tomhogue/Digital_Carb_Sync_Shield/CarbSync_CD_2015July/Pictures/before heating.JPG

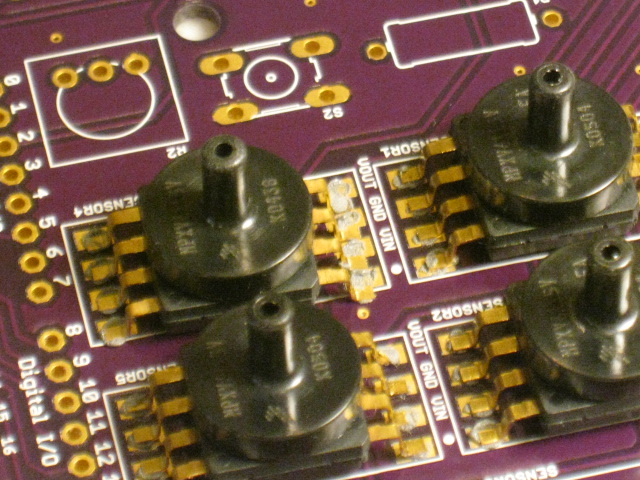
CarbSync_CD_2015July/Pictures/before heating.JPG
