tomhogue/Digital_Carb_Sync_Shield/CarbSync_CD_2015July/Pictures/complete x4.jpg

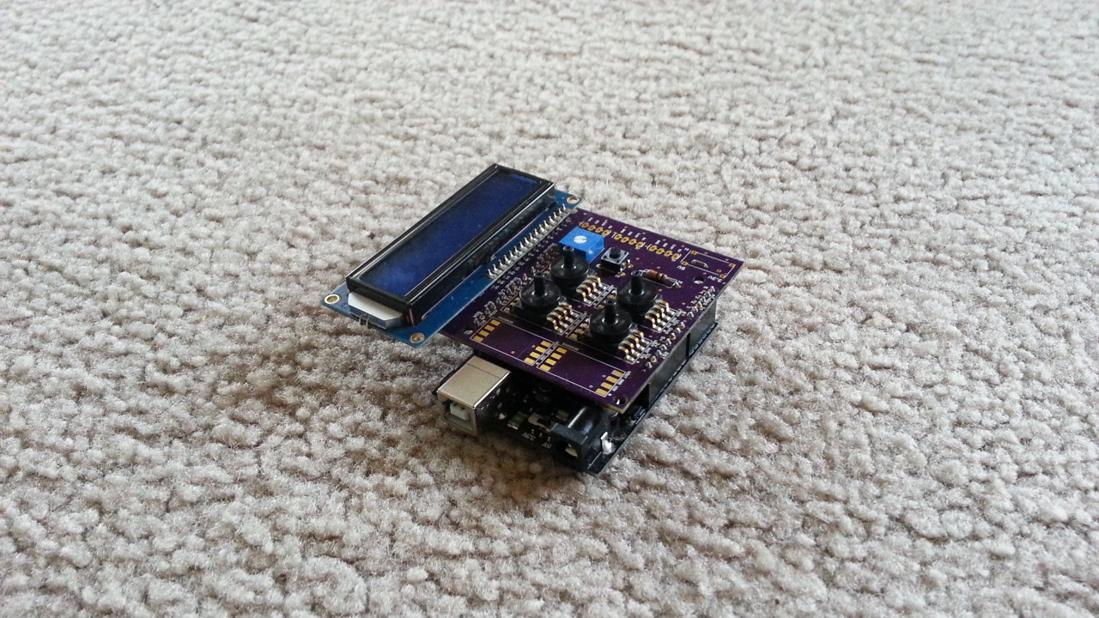
CarbSync_CD_2015July/Pictures/complete x4.jpg
