tomhogue/Digital_Carb_Sync_Shield/CarbSync_CD_2015July/Pictures/cooling.JPG

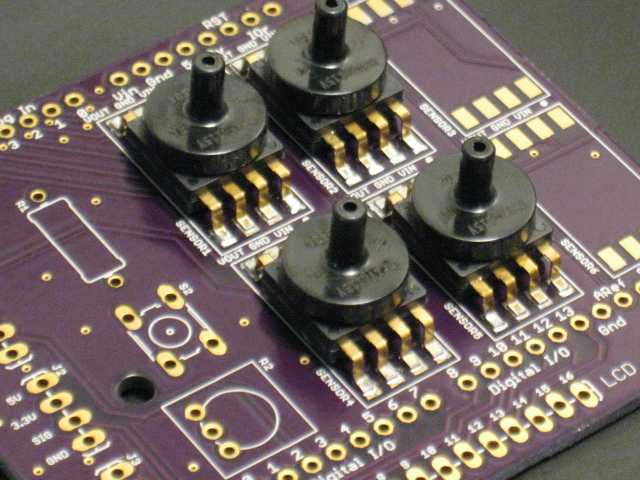
CarbSync_CD_2015July/Pictures/cooling.JPG
