tomhogue/Digital_Carb_Sync_Shield/CarbSync_CD_2015July/Pictures/headers to attach to UNO.JPG

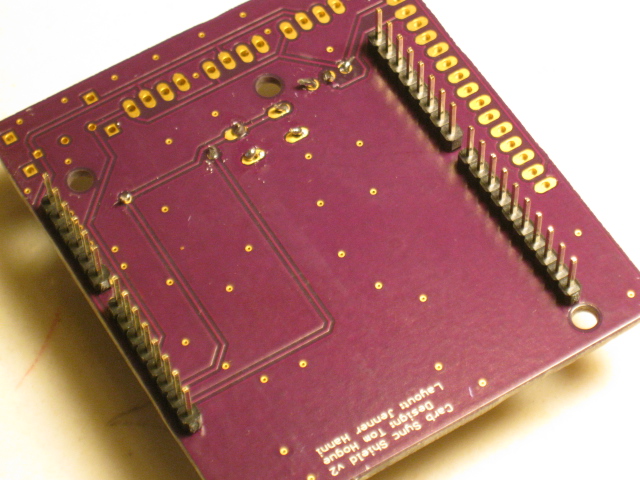
CarbSync_CD_2015July/Pictures/headers to attach to UNO.JPG
