tomhogue/Digital_Carb_Sync_Shield/CarbSync_CD_2015July/Pictures/IMG_0836.JPG

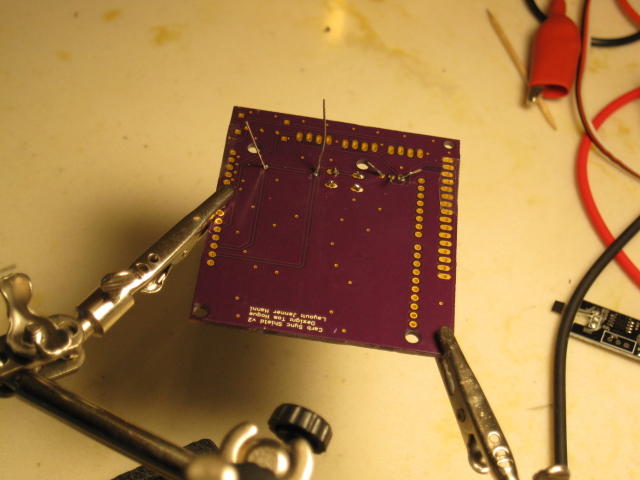
CarbSync_CD_2015July/Pictures/IMG_0836.JPG
