tomhogue/Digital_Carb_Sync_Shield/CarbSync_CD_2015July/Pictures/in use 02.JPG

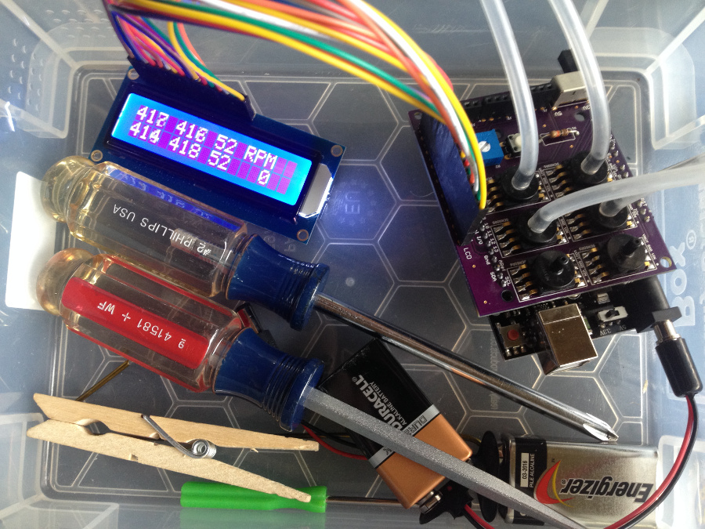
CarbSync_CD_2015July/Pictures/in use 02.JPG
