tomhogue/Digital_Carb_Sync_Shield/CarbSync_CD_2015July/Pictures/joints.gif

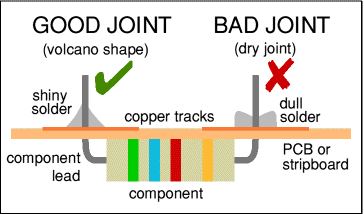
CarbSync_CD_2015July/Pictures/joints.gif
