tomhogue/Digital_Carb_Sync_Shield/CarbSync_CD_2015July/Pictures/Notch and dot.JPG

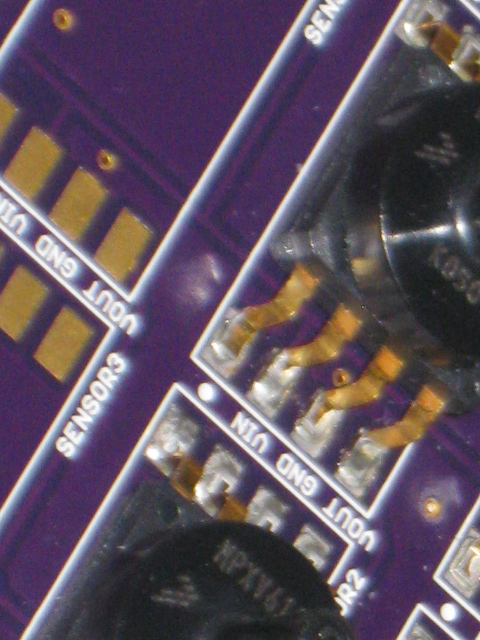
CarbSync_CD_2015July/Pictures/Notch and dot.JPG
