tomhogue/Digital_Carb_Sync_Shield/CarbSync_CD_2015July/Pictures/powered up 2015.jpg

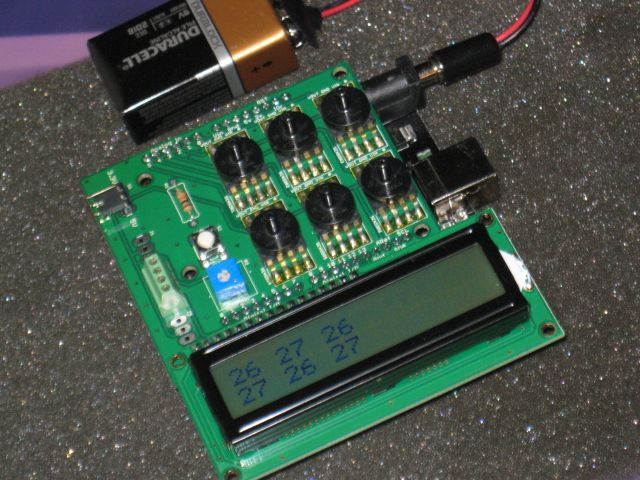
CarbSync_CD_2015July/Pictures/powered up 2015.jpg
