tomhogue/Digital_Carb_Sync_Shield/CarbSync_CD_2015July/Pictures/Header_Joints_guide.jpg

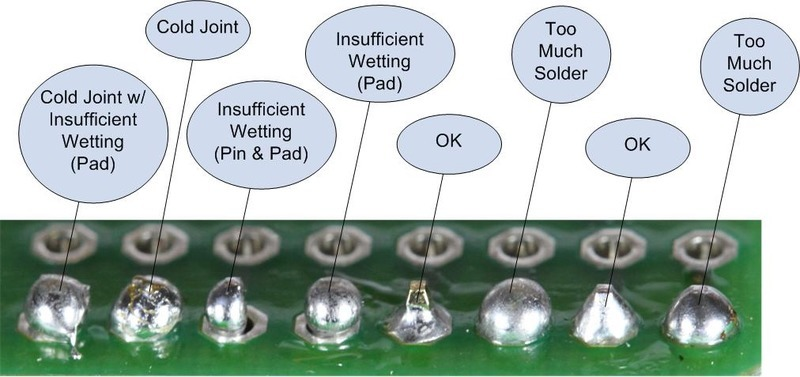
CarbSync_CD_2015July/Pictures/Header_Joints_guide.jpg
