tomhogue/Digital_Carb_Sync_Shield/CarbSync_CD_2015July/Pictures/hot plate and solder paste.JPG

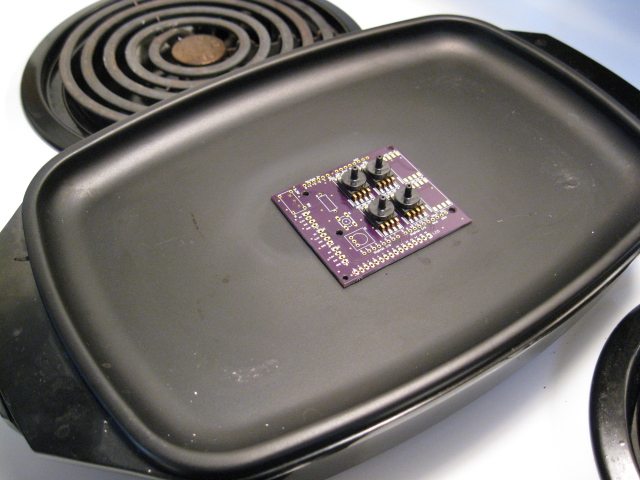
CarbSync_CD_2015July/Pictures/hot plate and solder paste.JPG
