tomhogue/Digital_Carb_Sync_Shield/CarbSync_CD_2015July/Pictures/solder joint diagram.gif

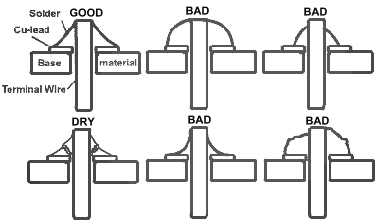
CarbSync_CD_2015July/Pictures/solder joint diagram.gif
