tomhogue/Digital_Carb_Sync_Shield/CarbSync_CD_2015July/Pictures/solder paste application.JPG

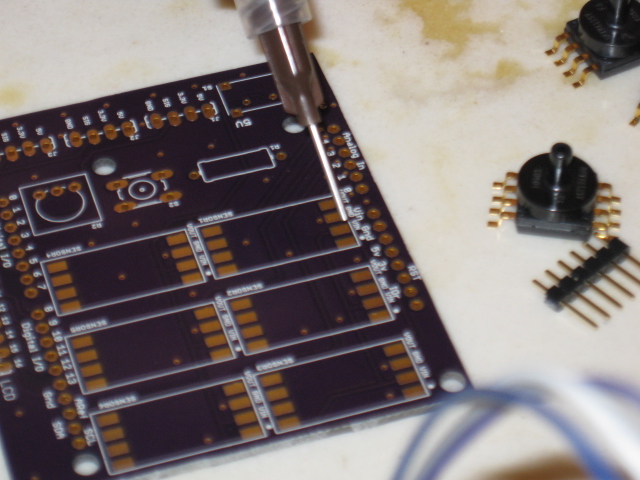
CarbSync_CD_2015July/Pictures/solder paste application.JPG
